auomoto/ATtiny4313_PN532/hardware/ATtiny4313_PN532.sch

## EAGLE design hardware/ATtiny4313_PN532.sch (2014-01-16)

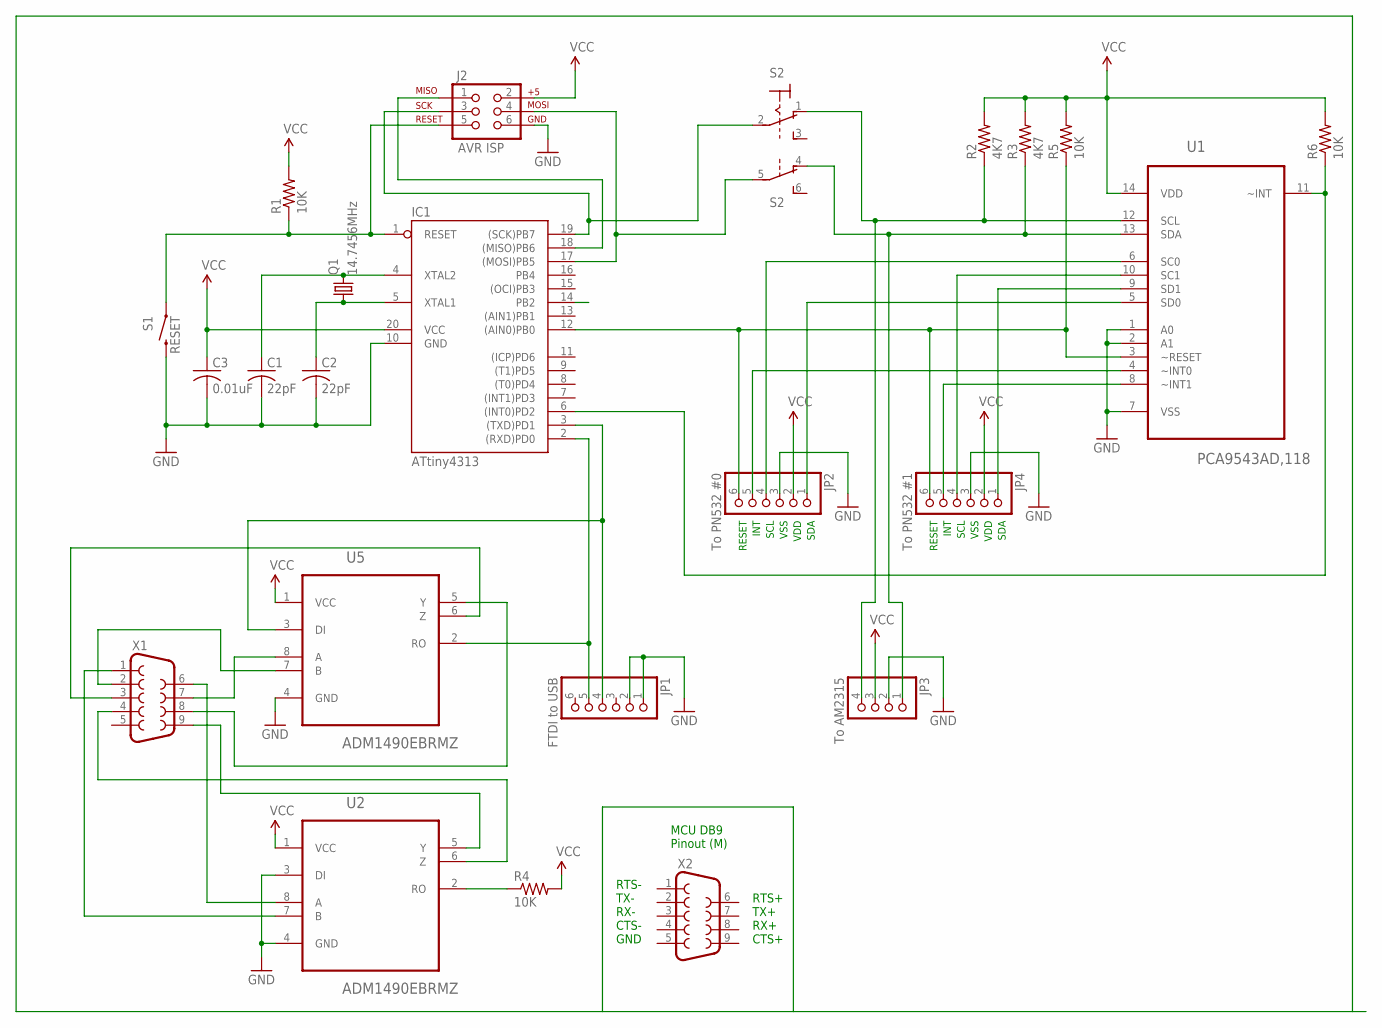
[picture p6: schematic ATtiny4313_PN532.sch]

Parts:
C1, C2: 22pF; C025-024X044
C3: 0.01uF; C025-024X044
IC1: ATtiny4313; DIL20
J2: AVR ISP; 2X3
JP1: FTDI to USB; 1X06/90
JP2: To PN532 #0; 1X06/90
JP3: To AM2315; 1X04/90
JP4: To PN532 #1; 1X06/90
Q1: 14.7456MHz; HC49U-V
R1, R4, R5, R6: 10K; 0204V
R2, R3: 4K7; 0204V
S1: RESET; TACTILE-PTH
S2: 320-938
U1: PCA9543AD,118; SOIC127P600X175-14N
U2, U5: ADM1490EBRMZ; SOP65P490X110-8N
X1, X2: DB9MALE; DB9_MALE

Connections:
GND: C1.2, C2.2, C3.2, IC1.10 (GND), J2.6, JP1.1, JP1.2, JP2.3, JP3.2, JP4.3, S1.3 (2), U1.1 (A0), U1.2 (A1), U1.7 (VSS), U2.3 (DI), U2.4 (GND), U5.4 (GND)
unnamed: IC1.1 (RESET), J2.5, R1.1, S1.1
unnamed: C2.1, IC1.5 (XTAL1), Q1.1
unnamed: IC1.3 ((TXD)PD1), JP1.4, U5.3 (DI)
unnamed: IC1.2 ((RXD)PD0), JP1.5, U5.2 (RO)
unnamed: U5.6 (Z), X1.3
unnamed: C1.1, IC1.4 (XTAL2), Q1.2
unnamed: R4.1, U2.2 (RO)
unnamed: IC1.6 ((INT0)PD2), R6.1, U1.11 (~INT)
unnamed: JP2.1, U1.5 (SD0)
unnamed: JP2.4, U1.6 (SC0)
unnamed: JP4.1, U1.9 (SD1)
unnamed: JP4.4, U1.10 (SC1)
unnamed: IC1.12 ((AIN0)PB0), JP2.6, JP4.6, R5.1, U1.3 (~RESET)
unnamed: IC1.18 ((MISO)PB6), J2.1
unnamed: JP2.5, U1.4 (~INT0)
unnamed: U5.8 (A), X1.7
unnamed: JP4.5, U1.8 (~INT1)
unnamed: U5.7 (B), X1.2
unnamed: U2.5 (Y), X1.9
unnamed: U5.5 (Y), X1.8
unnamed: U2.6 (Z), X1.4
unnamed: U2.8 (A), X1.6
unnamed: U2.7 (B), X1.1
unnamed: JP3.4, R2.1, S2.1 (O), U1.12 (SCL)
unnamed: JP3.1, R3.1, S2.4 (O), U1.13 (SDA)
SCL: IC1.19 ((SCK)PB7), J2.3, S2.2
SDA: IC1.17 ((MOSI)PB5), J2.4, S2.5
VCC: C3.1, IC1.20 (VCC), J2.2, JP2.2, JP3.3, JP4.2, R1.2, R2.2, R3.2, R4.2, R5.2, R6.2, U1.14 (VDD), U2.1 (VCC), U5.1 (VCC)

Notes on the sheet:
SDA
VDD
VSS
SCL
INT
RESET
RTS-
TX-
RX-
CTS-
GND
RTS+
TX+
RX+
CTS+
MCU DB9 Pinout (M)
