auomoto/ATtiny4313_PN532/hardware/ATtiny4313_PN532_Cable.sch

## EAGLE design hardware/ATtiny4313_PN532_Cable.sch (2014-01-16)

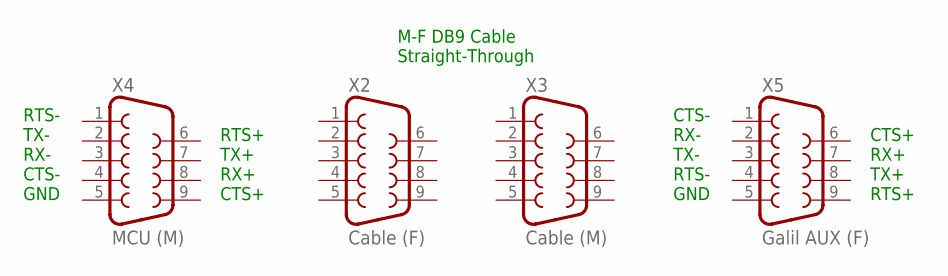
[picture p7: schematic ATtiny4313_PN532_Cable.sch]

Parts:
X2: Cable (F); DB9
X3: Cable (M); DB9_MALE
X4: MCU (M); DB9_MALE
X5: Galil AUX (F); DB9

Notes on the sheet:
CTS-
RX-
TX-
RTS-
GND
CTS+
RX+
TX+
RTS+
M-F DB9 Cable Straight-Through
